Wake-Up-It-s-a-Hospital/HW/3D modeling/smart wearable device/견적서/2층 pcb 설게도.png

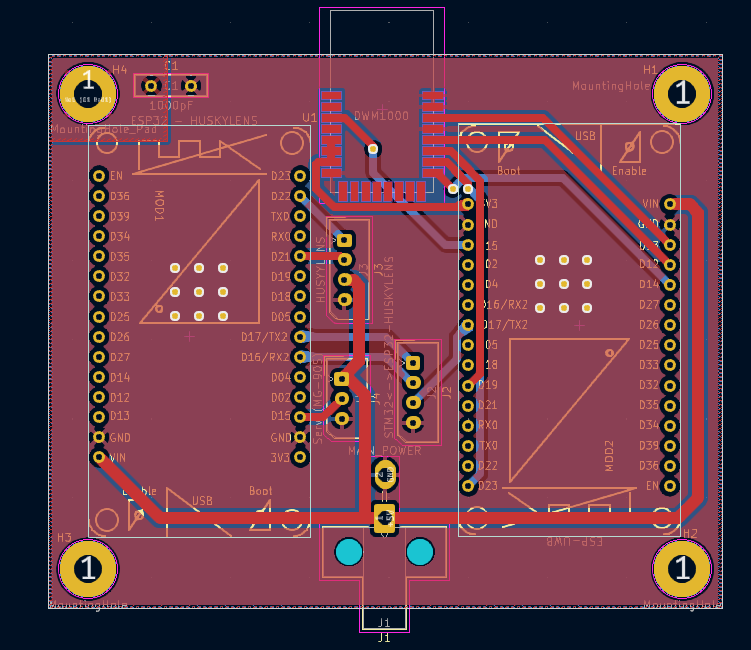
3D modeling/smart wearable device/견적서/2층 pcb 설게도.png
