Wake-Up-It-s-a-Hospital/HW/프로파일/3번프로파일.jpg

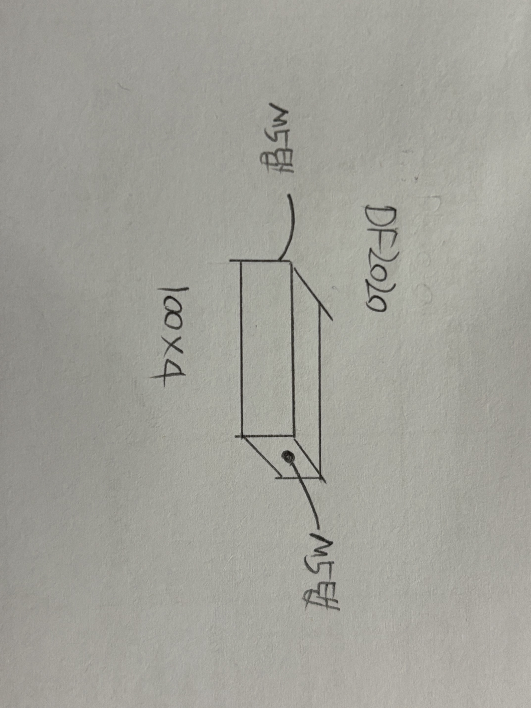
프로파일/3번프로파일.jpg
