Wake-Up-It-s-a-Hospital/HW/3D modeling/4층 모델링/4thfloor_bracket 본체.3mf

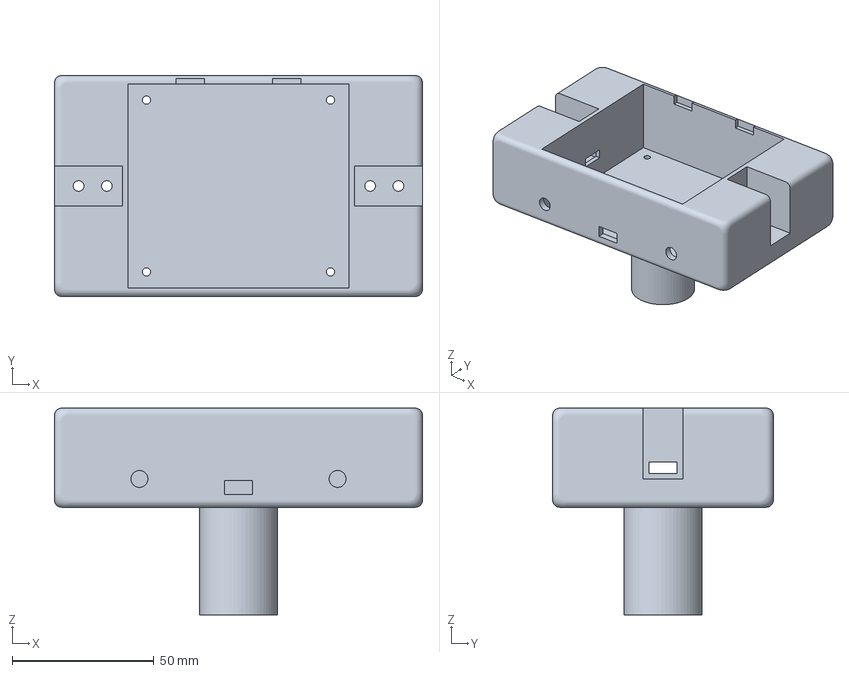
[picture p26: CAD file, 2025-08-07]
3D modeling/4층 모델링/4thfloor_bracket 본체.3mf
130.0 x 78.0 x 73.0 mm
