Wake-Up-It-s-a-Hospital/HW/아크릴/B.dxf

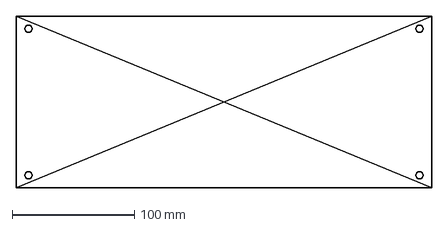
[picture p27: CAD file, 2025-05-25]
아크릴/B.dxf
340.0 x 140.0 mm
