Wake-Up-It-s-a-Hospital/HW/프로파일/2번프로파일.jpg

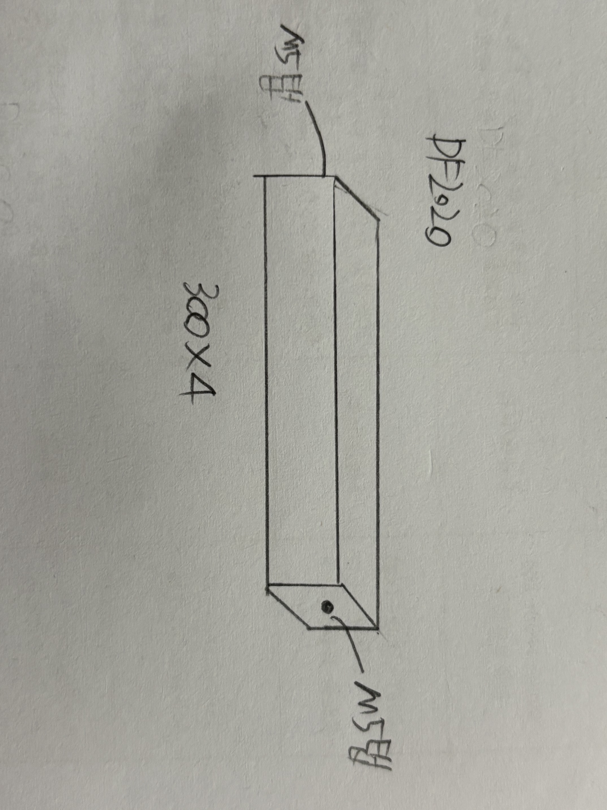
프로파일/2번프로파일.jpg
