Wake-Up-It-s-a-Hospital/HW/프로파일/전체 프로파일들.jpg

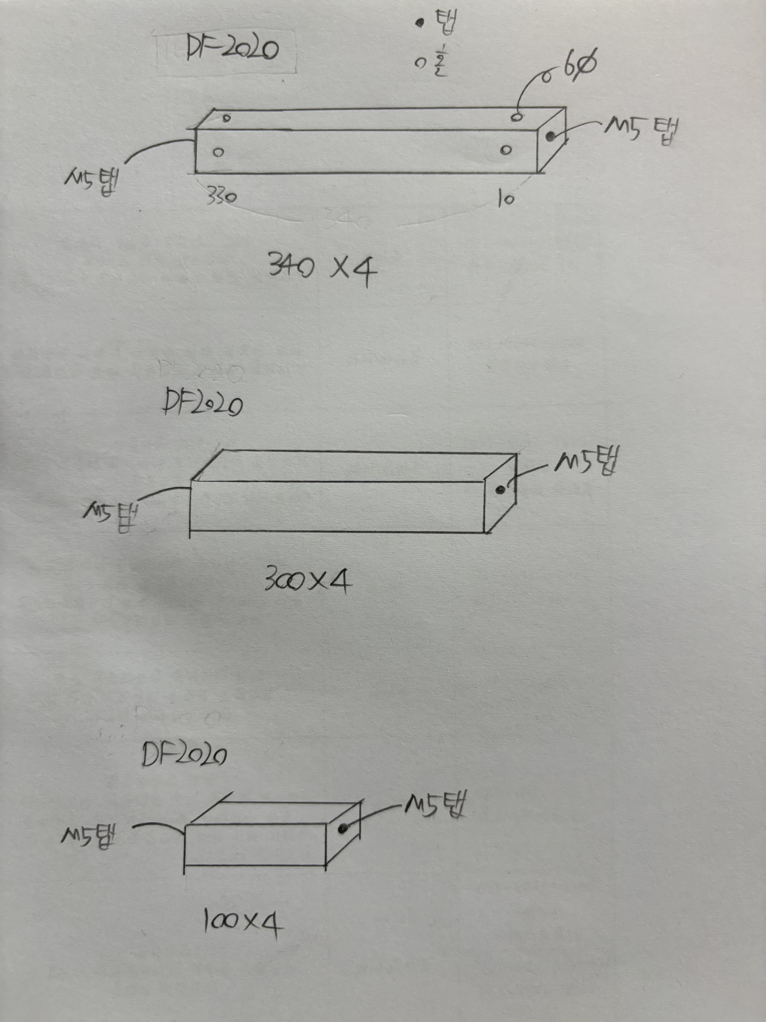
프로파일/전체 프로파일들.jpg
